acastles91/narcise/scriptTestTest.h

## File generated on 2021-03-24 11:08:53.131016
std::vector<vector<int>> finalLines;
std::vector<int>    line_0 = { 100, 0, 30, 20, 100, 80, 0, 0, 100, 90 };
finalLines.pushback(line_0);
std::vector<int>    line_1 = { 98, 2, 30, 21, 97, 80, 3, 2, 97, 88 };
finalLines.pushback(line_1);
std::vector<int>    line_2 = { 97, 5, 29, 21, 94, 81, 7, 3, 93, 85 };
finalLines.pushback(line_2);
std::vector<int>    line_3 = { 95, 8, 28, 22, 91, 81, 10, 5, 90, 83 };
finalLines.pushback(line_3);
std::vector<int>    line_4 = { 93, 10, 28, 23, 88, 81, 13, 7, 87, 81 };
finalLines.pushback(line_4);
std::vector<int>    line_5 = { 92, 12, 28, 23, 85, 82, 17, 8, 83, 78 };
finalLines.pushback(line_5);
std::vector<int>    line_6 = { 90, 15, 27, 24, 82, 82, 20, 10, 80, 76 };
finalLines.pushback(line_6);
std::vector<int>    line_7 = { 88, 18, 26, 25, 79, 82, 23, 12, 77, 74 };
finalLines.pushback(line_7);
std::vector<int>    line_8 = { 87, 20, 26, 25, 76, 83, 27, 13, 73, 71 };
finalLines.pushback(line_8);
std::vector<int>    line_9 = { 85, 22, 26, 26, 73, 83, 30, 15, 70, 69 };
finalLines.pushback(line_9);
std::vector<int>    line_10 = { 83, 25, 25, 27, 70, 83, 33, 17, 67, 67 };
finalLines.pushback(line_10);
std::vector<int>    line_11 = { 82, 28, 24, 27, 67, 84, 37, 18, 63, 64 };
finalLines.pushback(line_11);
std::vector<int>    line_12 = { 80, 30, 24, 28, 64, 84, 40, 20, 60, 62 };
finalLines.pushback(line_12);
std::vector<int>    line_13 = { 78, 32, 24, 29, 61, 84, 43, 22, 57, 60 };
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
finalLines.pushback(line_1116);
std::vector<int>    line_1117 = { 59, 38, 31, 28, 42, 13, 21, 29, 87, 76 };
finalLines.pushback(line_1117);
std::vector<int>    line_1118 = { 59, 38, 31, 28, 42, 13, 21, 29, 87, 76 };
finalLines.pushback(line_1118);
std::vector<int>    line_1119 = { 59, 38, 31, 28, 42, 13, 21, 29, 87, 76 };
finalLines.pushback(line_1119);
std::vector<int>    line_1120 = { 59, 38, 31, 28, 42, 13, 21, 29, 87, 76 };
finalLines.pushback(line_1120);
std::vector<int>    line_1121 = { 59, 38, 31, 28, 42, 13, 21, 29, 87, 76 };
finalLines.pushback(line_1121);
std::vector<int>    line_1122 = { 59, 38, 31, 28, 42, 13, 21, 29, 87, 75 };
finalLines.pushback(line_1122);
std::vector<int>    line_1123 = { 59, 38, 31, 28, 42, 13, 21, 29, 87, 75 };
finalLines.pushback(line_1123);
std::vector<int>    line_1124 = { 59, 38, 31, 28, 42, 13, 21, 29, 87, 75 };
finalLines.pushback(line_1124);
std::vector<int>    line_1125 = { 59, 38, 31, 28, 42, 13, 21, 29, 87, 75 };
finalLines.pushback(line_1125);
std::vector<int>    line_1126 = { 59, 38, 31, 28, 42, 13, 21, 29, 87, 75 };
finalLines.pushback(line_1126);
std::vector<int>    line_1127 = { 59, 38, 31, 28, 42, 13, 21, 29, 87, 75 };
finalLines.pushback(line_1127);
std::vector<int>    line_1128 = { 59, 38, 31, 28, 42, 13, 21, 29, 87, 75 };
finalLines.pushback(line_1128);
std::vector<int>    line_1129 = { 59, 38, 31, 28, 42, 13, 21, 29, 87, 75 };
finalLines.pushback(line_1129);
std::vector<int>    line_1130 = { 59, 38, 31, 28, 42, 13, 21, 29, 87, 75 };
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
